atopile/nonos/elec/src/parts/STMicroelectronics_ESDA25W/SOT-323-3_L2.0-W1.3-H1.0-LS2.1-P1.30.step

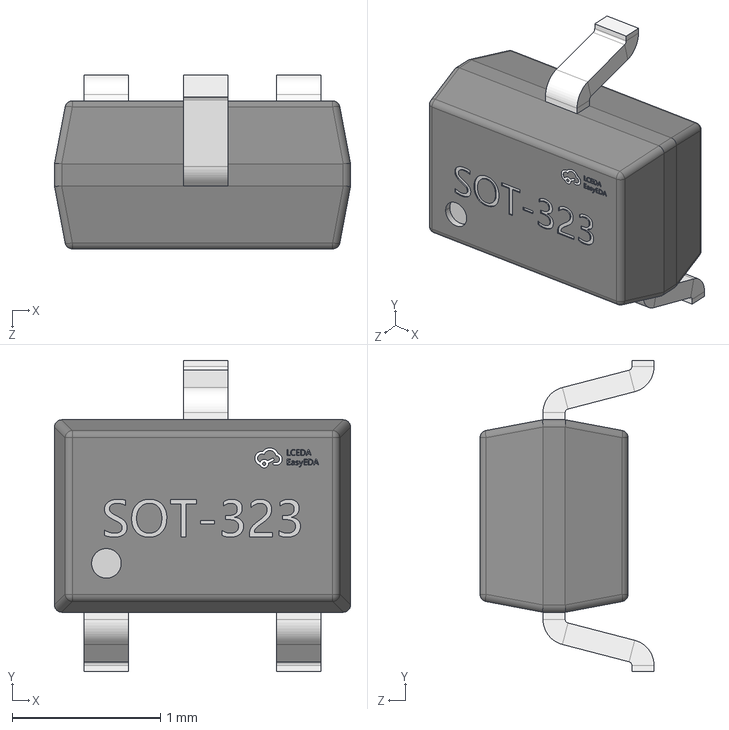
[picture p21: CAD file, 2024-11-20]
elec/src/parts/STMicroelectronics_ESDA25W/SOT-323-3_L2.0-W1.3-H1.0-LS2.1-P1.30.step
2.00 x 2.10 x 1.18 mm
