atopile/nonos/elec/src/parts/STMicroelectronics_STPS340U/SMB_L4.6-W3.6-LS5.3-RD.step

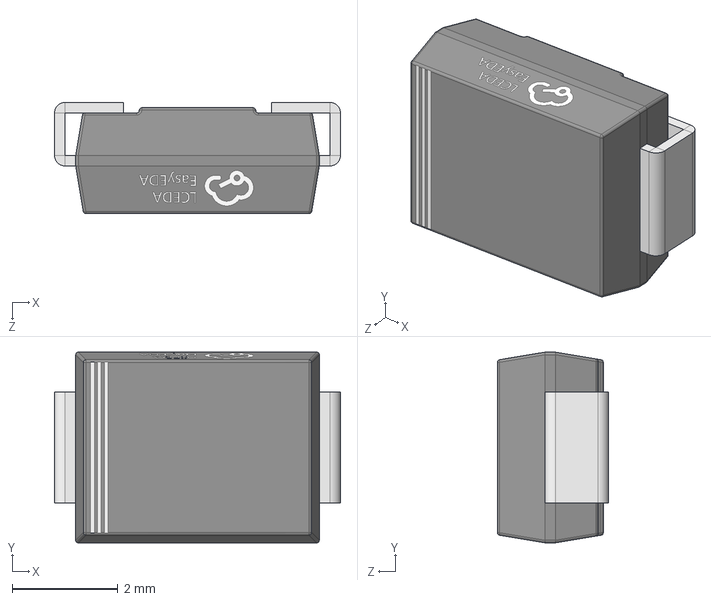
[picture p22: CAD file, 2025-07-16]
elec/src/parts/STMicroelectronics_STPS340U/SMB_L4.6-W3.6-LS5.3-RD.step
5.40 x 3.60 x 2.10 mm
