atopile/nonos/elec/src/parts/STMicroelectronics_STUSB4500QTR/57.STEP

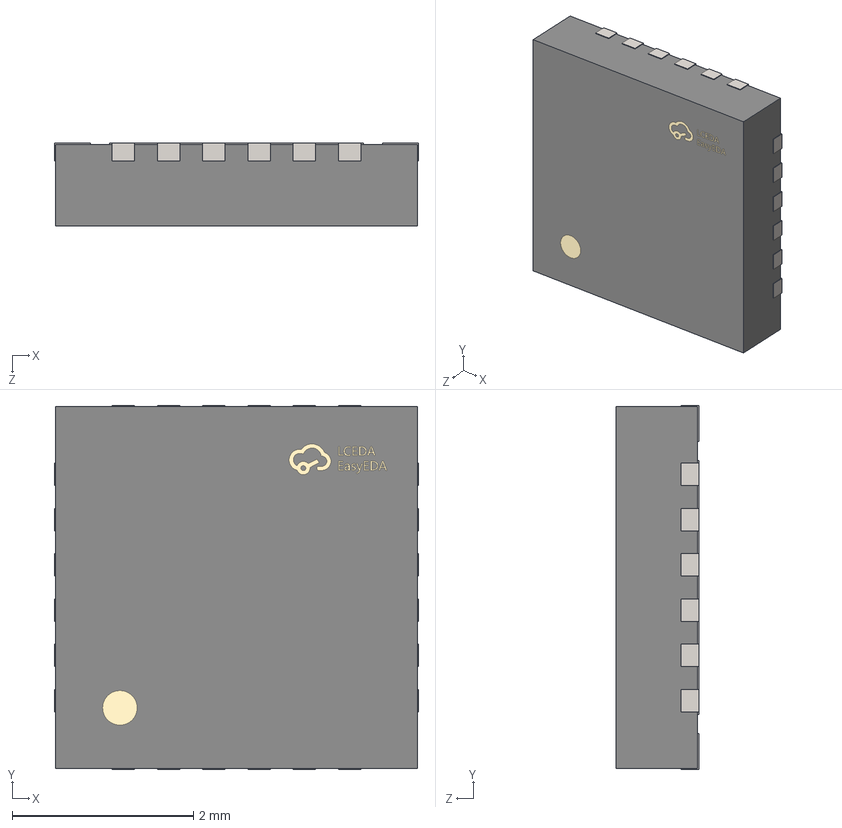
[picture p23: CAD file, 2024-11-20]
elec/src/parts/STMicroelectronics_STUSB4500QTR/57.STEP
4.02 x 4.02 x 0.92 mm
