atopile/nonos/elec/src/parts/Sunlord_SWPA8040S5R6NT/IND-SMD_L8.0-W8.0-H4.2.STEP

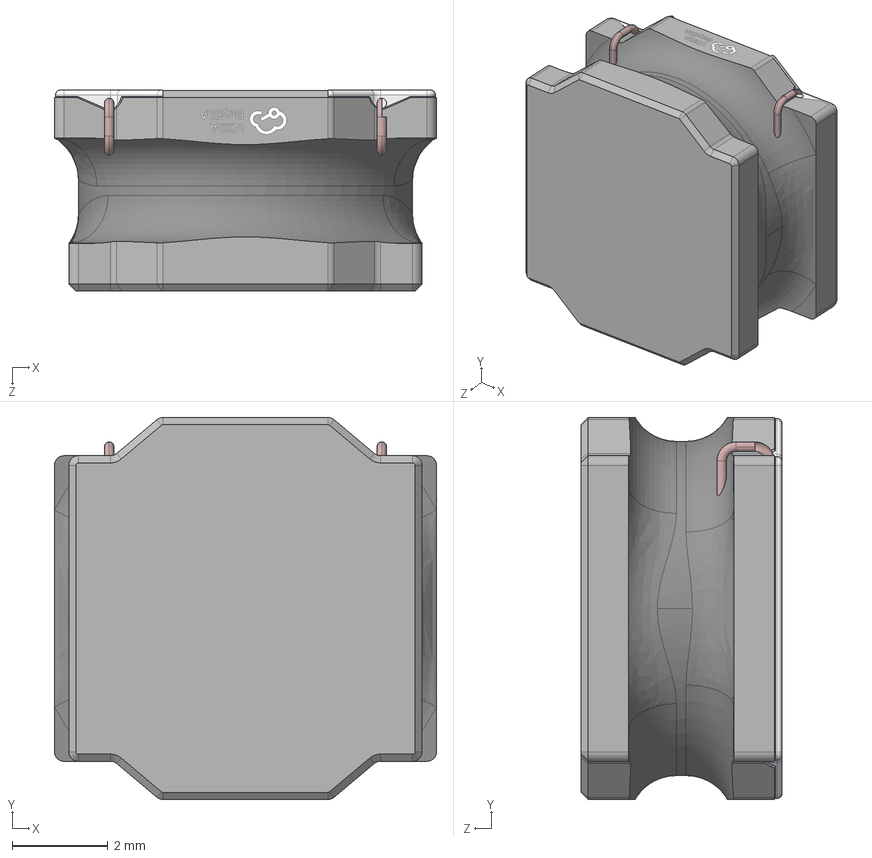
[picture p24: CAD file, 2025-07-16]
elec/src/parts/Sunlord_SWPA8040S5R6NT/IND-SMD_L8.0-W8.0-H4.2.STEP
8.00 x 8.00 x 4.21 mm
