atopile/nonos/elec/src/parts/TDK_NLV32T_R56J_EF/IND-SMD_L3.2-W2.5.step

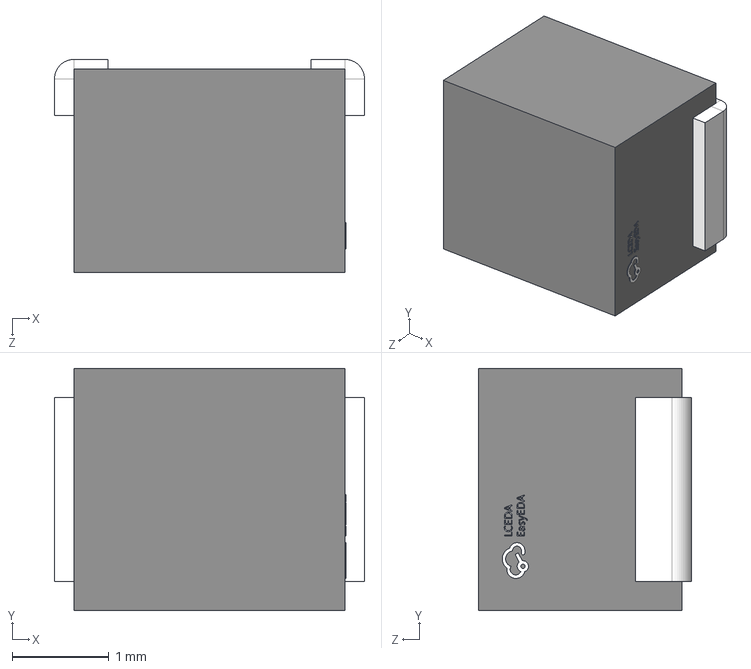
[picture p25: CAD file, 2025-08-16]
elec/src/parts/TDK_NLV32T_R56J_EF/IND-SMD_L3.2-W2.5.step
3.20 x 2.50 x 2.20 mm
