atopile/nonos/elec/src/parts/TE_Connectivity_1_2328702_0/FPC-SMD_10P-P0.50_HDGC_0.5K-HX-10PWB.step

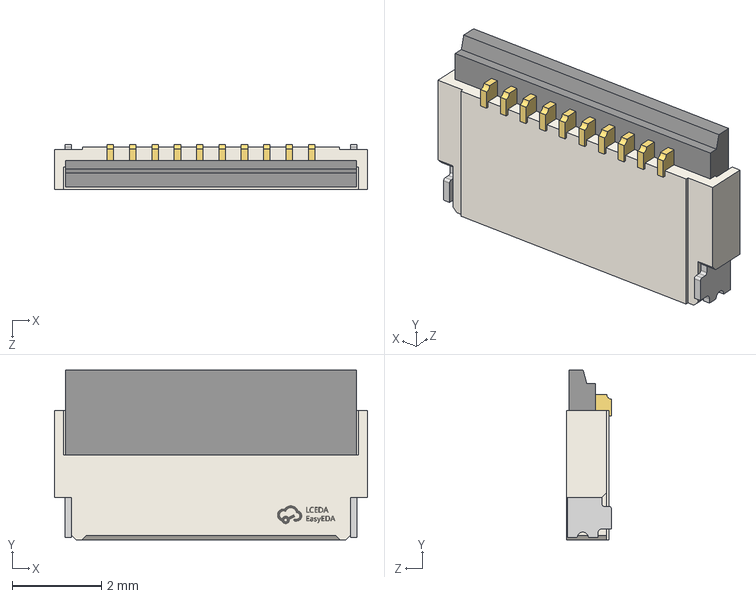
[picture p26: CAD file, 2025-07-03]
elec/src/parts/TE_Connectivity_1_2328702_0/FPC-SMD_10P-P0.50_HDGC_0.5K-HX-10PWB.step
7.00 x 3.80 x 1.00 mm
