atopile/nonos/elec/src/parts/Texas_Instruments_SN74LVC1G07DBVR/SOT-23-5_L2.9-W1.6-H1.1-LS2.8-P0.95.step

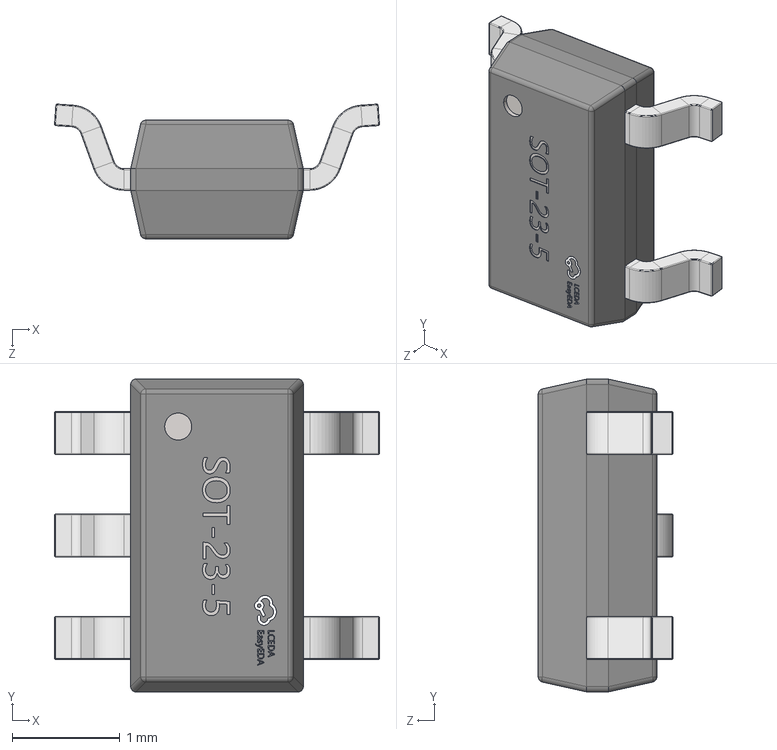
[picture p27: CAD file, 2025-07-16]
elec/src/parts/Texas_Instruments_SN74LVC1G07DBVR/SOT-23-5_L2.9-W1.6-H1.1-LS2.8-P0.95.step
3.01 x 2.90 x 1.25 mm
