atopile/nonos/elec/src/parts/Texas_Instruments_TLV75901PDRVR/WSON-6_L2.0-W2.0-H0.8-P0.65.step

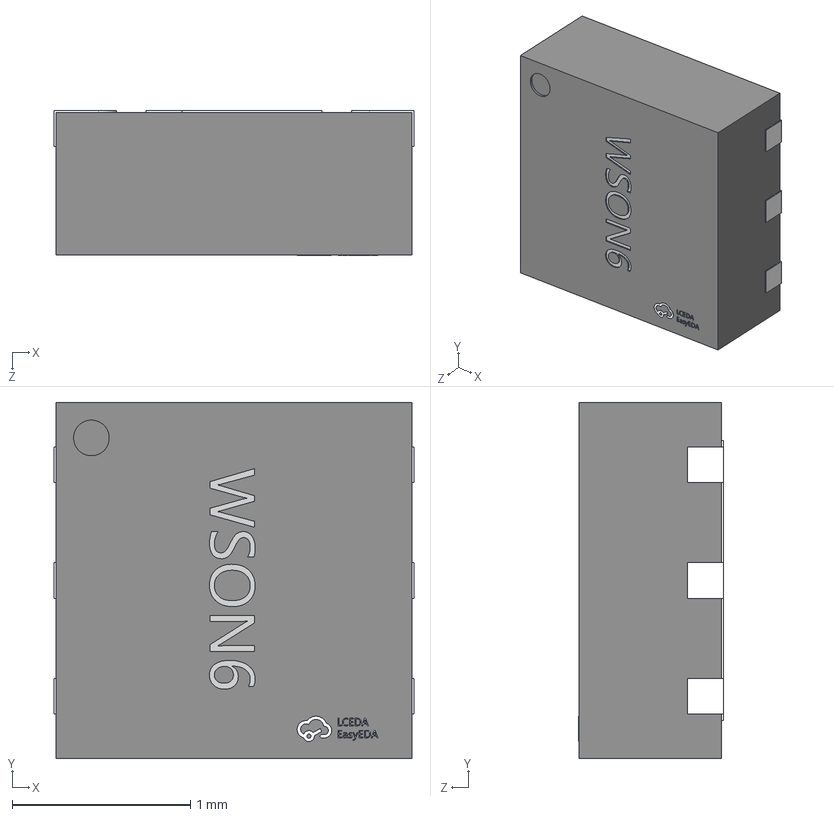
[picture p28: CAD file, 2025-07-16]
elec/src/parts/Texas_Instruments_TLV75901PDRVR/WSON-6_L2.0-W2.0-H0.8-P0.65.step
2.02 x 2.00 x 0.811 mm
