atopile/nonos/elec/src/parts/Texas_Instruments_TPS54560DDAR/SOIC-8_L4.9-W3.9-H1.7-LS6.0-P1.27.step

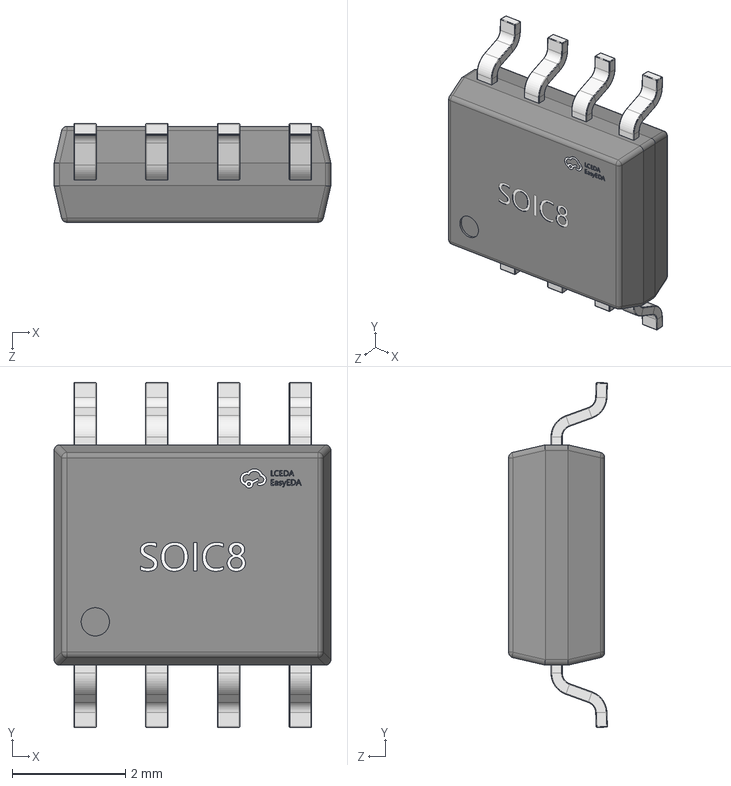
[picture p29: CAD file, 2025-07-16]
elec/src/parts/Texas_Instruments_TPS54560DDAR/SOIC-8_L4.9-W3.9-H1.7-LS6.0-P1.27.step
4.90 x 6.11 x 1.75 mm
