atopile/nonos/elec/src/parts/UNI_ROYAL_0402WGF4700TCE/R0402_L1.0-W0.5-H0.4.step

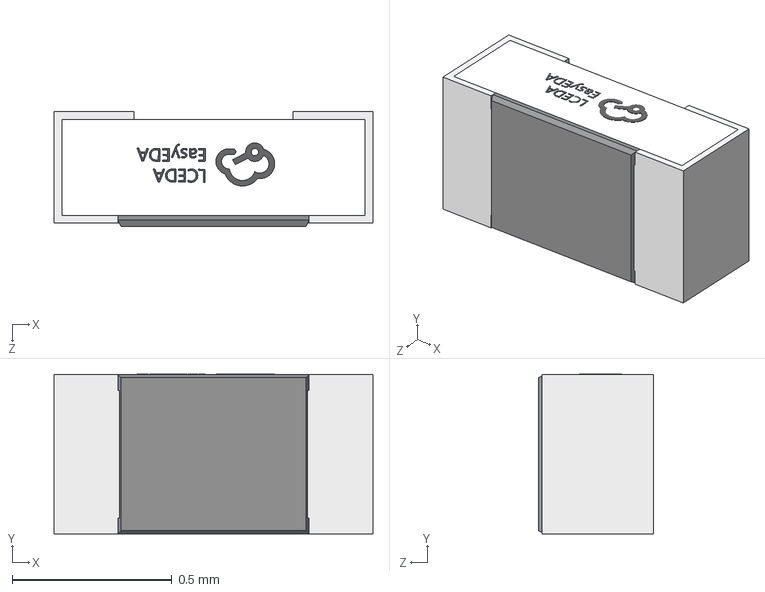
[picture p30: CAD file, 2025-07-03]
elec/src/parts/UNI_ROYAL_0402WGF4700TCE/R0402_L1.0-W0.5-H0.4.step
1.00 x 0.501 x 0.36 mm
