atopile/nonos/elec/src/parts/UNI_ROYAL_0603WAF0000T5E/R0603.STEP

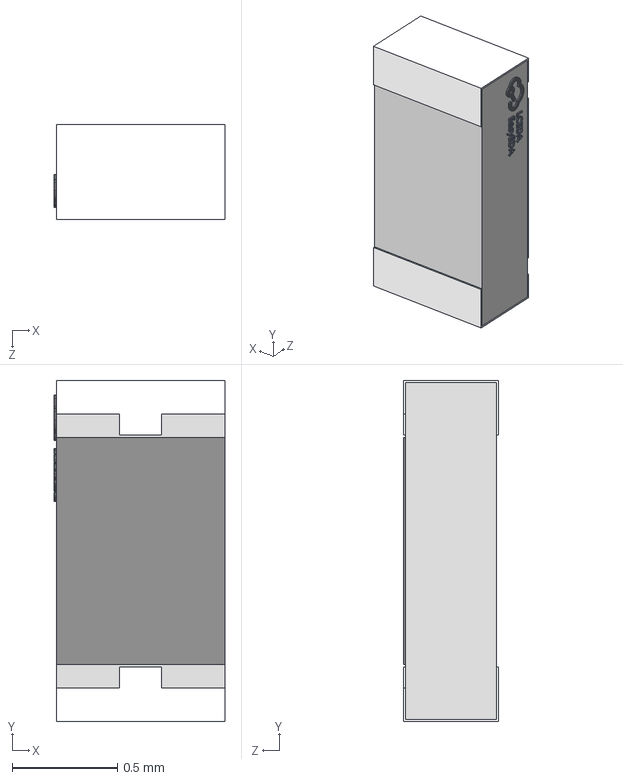
[picture p31: CAD file, 2024-11-27]
elec/src/parts/UNI_ROYAL_0603WAF0000T5E/R0603.STEP
0.81 x 1.62 x 0.45 mm
