atopile/nonos/elec/src/parts/XKB_Connectivity_TS_1101_C_W/SW-SMD_L6.0-W3.3-H5-LS8.0.step

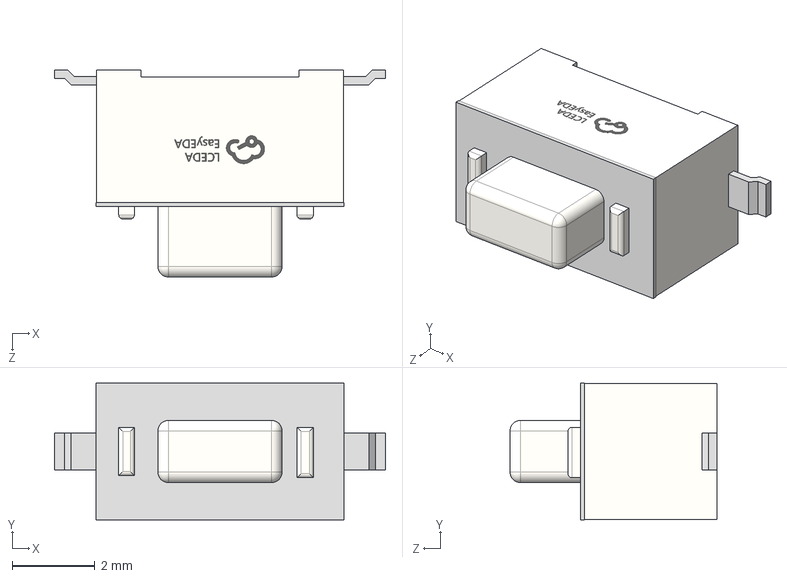
[picture p32: CAD file, 2025-07-16]
elec/src/parts/XKB_Connectivity_TS_1101_C_W/SW-SMD_L6.0-W3.3-H5-LS8.0.step
8.00 x 3.30 x 5.00 mm
