atopile/nonos/elec/src/parts/XKB_Connectivity_U262_241N_4BV64/USB-C-SMD_TYC-324G.step

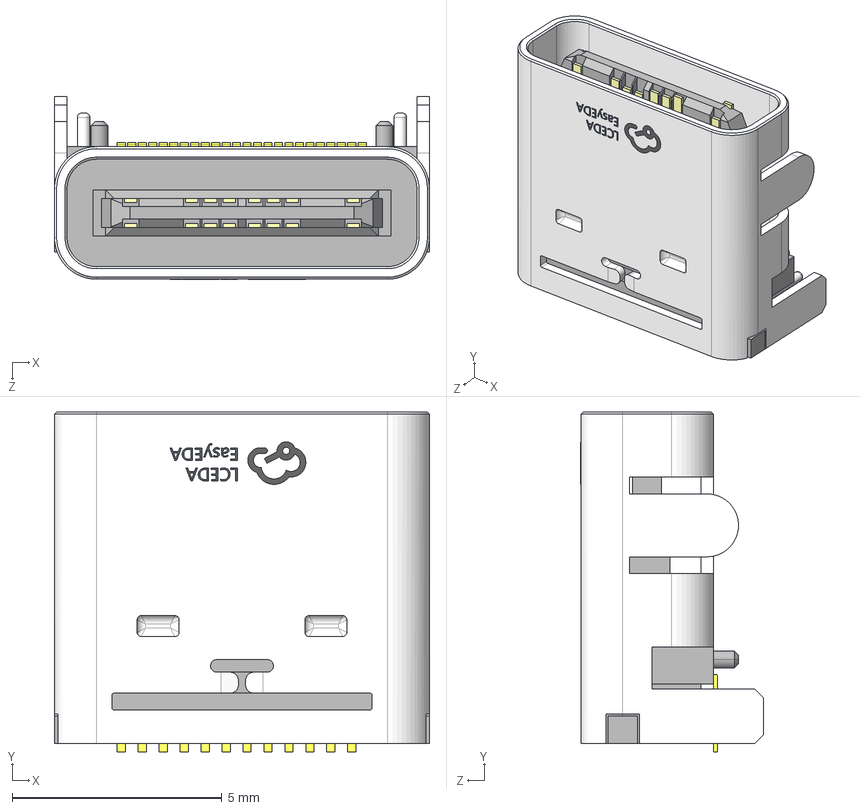
[picture p33: CAD file, 2025-07-16]
elec/src/parts/XKB_Connectivity_U262_241N_4BV64/USB-C-SMD_TYC-324G.step
8.94 x 8.10 x 4.35 mm
