atopile/nonos/firmware/nonos_server/src/audio_server/bt-agent.py

#!/usr/bin/env python3
import dbus
import dbus.mainloop.glib
import dbus.service
from gi.repository import GLib

AGENT_PATH = "/test/agent"


class Agent(dbus.service.Object):
    @dbus.service.method("org.bluez.Agent1", in_signature="", out_signature="")
    def Release(self):
        pass

    @dbus.service.method("org.bluez.Agent1", in_signature="o", out_signature="")
    def RequestAuthorization(self, device):
        return

    @dbus.service.method("org.bluez.Agent1", in_signature="os", out_signature="")
    def AuthorizeService(self, device, uuid):
        print(f"Authorizing service {uuid} from {device}")
        return

    @dbus.service.method("org.bluez.Agent1", in_signature="o", out_signature="s")
    def RequestPinCode(self, device):
        return "0000"

    @dbus.service.method("org.bluez.Agent1", in_signature="o", out_signature="u")
    def RequestPasskey(self, device):
        return dbus.UInt32(123456)

    @dbus.service.method("org.bluez.Agent1", in_signature="ouq", out_signature="")
    def DisplayPasskey(self, device, passkey, entered):
        pass

    @dbus.service.method("org.bluez.Agent1", in_signature="o", out_signature="")
    def RequestConfirmation(self, device):
        return

    @dbus.service.method("org.bluez.Agent1", in_signature="", out_signature="")
    def Cancel(self):
        pass


dbus.mainloop.glib.DBusGMainLoop(set_as_default=True)
bus = dbus.SystemBus()
agent = Agent(bus, AGENT_PATH)

manager = dbus.Interface(
    bus.get_object("org.bluez", "/org/bluez"), "org.bluez.AgentManager1"
)
manager.RegisterAgent(AGENT_PATH, "NoInputNoOutput")
manager.RequestDefaultAgent(AGENT_PATH)

print("Bluetooth auto-agent running...")
GLib.MainLoop().run()
